candyman570/ReadCO2/PCB/ReadCO2/ReadCO2.sch

## KiCad design PCB/ReadCO2/ReadCO2.sch (2020-11-28)

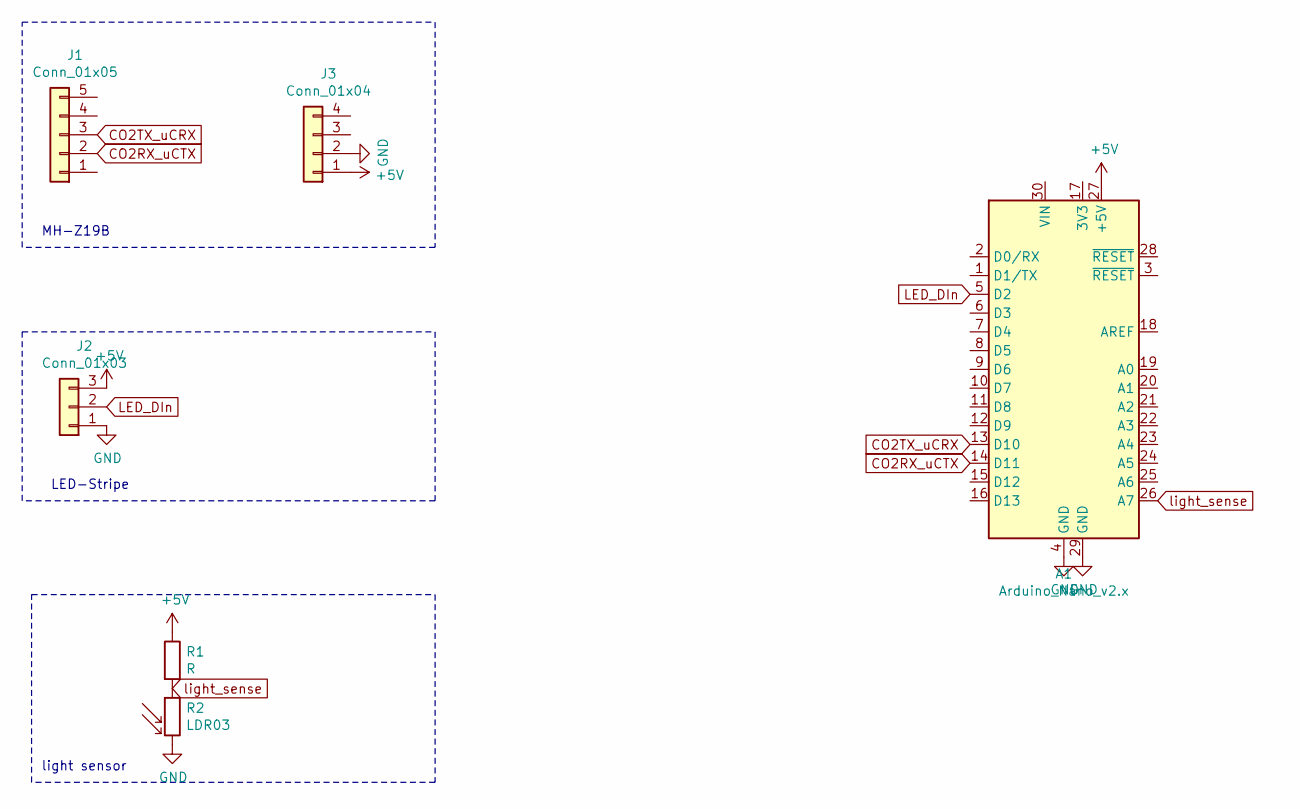
[picture p5: schematic ReadCO2.sch]

Parts:
A1: Arduino_Nano_v2.x; Arduino_Nano
J1: Conn_01x05; PinHeader_1x05_P2.54mm_Vertical
J2: Conn_01x03; PinHeader_1x03_P2.54mm_Vertical
J3: Conn_01x04; PinHeader_1x04_P2.54mm_Vertical
R1: R; R_Axial_DIN0207_L6.3mm_D2.5mm_P7.62mm_Horizontal
R2: LDR03; R_LDR_10x8.5mm_P7.6mm_Vertical

Connections:
+5V: A1.27 (+5V), J2.3, J3.1, R1.1
CO2RX_uCTX: A1.14 (D11), J1.2
CO2TX_uCRX: A1.13 (D10), J1.3
GND: A1.4 (GND), A1.29 (GND), J2.1, J3.2, R2.2
LED_DIn: A1.5 (D2), J2.2
light_sense: A1.26 (A7), R1.2, R2.1

Notes on the sheet:
MH-Z19B
LED-Stripe
light sensor
